ymt117/tane2019/Log/桃太郎ログ/2019-3-5-17-16-43/モータ出力.png

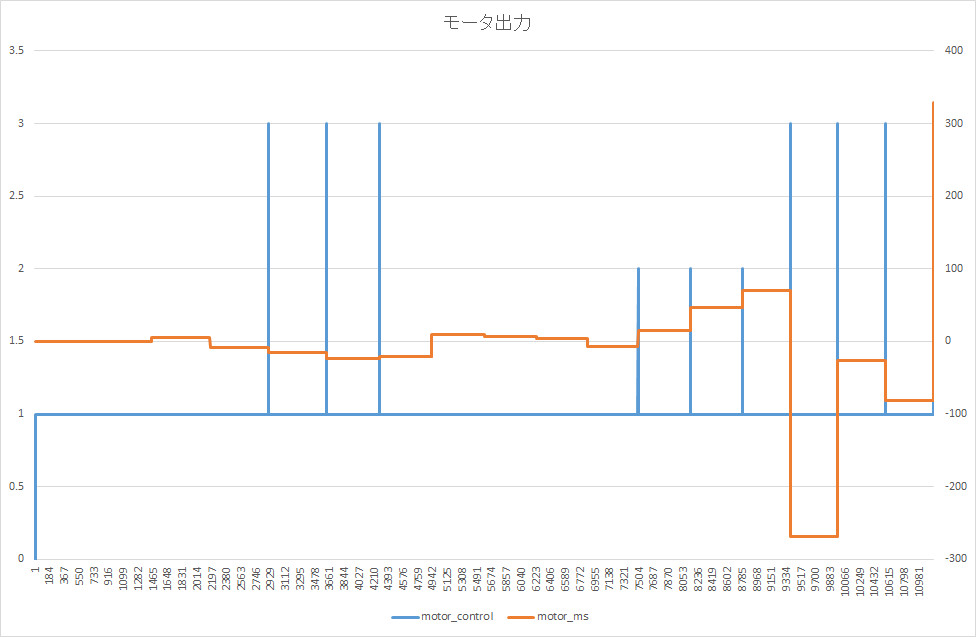
Log/桃太郎ログ/2019-3-5-17-16-43/モータ出力.png
