ymt117/tane2019/Src/mySD.h

// mySD.h
#ifndef MYSD_H_
#define MYSD_H_
#include <Arduino.h>
#include "FS.h"
#include "SD.h"
#include "SPI.h"

class mySD{
public:
  mySD();
  void listDir(fs::FS &fs, const char * dirname, uint8_t levels);
  void createDir(fs::FS &fs, const char * path);
  void removeDir(fs::FS &fs, const char * path);
  void readFile(fs::FS &fs, const char * path);
  void writeFile(fs::FS &fs, const char * path, const char *message);
  void appendFile(fs::FS &fs, const char * path, const char * message);
  void renameFile(fs::FS &fs, const char * path1, const char * path2);
  void deleteFile(fs::FS &fs, const char * path);
  void testFileIO(fs::FS &fs, const char * path);
};

#endif
